LieBtrau/AMT5000-24/simulation/amplifier/Class_E_with_transistor_and_gate_driver.asc

C1: cap; 255p
C2: cap; 715p
C3: cap; 185.30p
C4: cap; 555.89p
C5: cap; 555.89p
C7: cap; 10n
D1: diode; MMSD4148
L1: ind; .33µ
L2: ind; 190n
L3: ind; 5µ
M2: nmos; irlml2060pbf
M3: nmos; irlml2060pbf
R1: res; {Rout}
R2: res; 0.1
R3: res; {Rsource}
R4: res; 1k
R5: res; 48.5k
R6: res; 1.5k
U1: TS391
V1: voltage; 0; AC 1
V2: voltage; PULSE(0 5 0 1n 1n {0.5/freq} {1/freq})
V4: voltage; SINE(6 6 10k)
V5: voltage; 1.5v
Named nets: 0, VAC, VDD, OSC, NM0S_OUT4, Vref
;ac dec 101 1meg 1g
.model SWx SW(Ron=0.1 Roff=10Meg Vt=2.5 Vh=0.5)
.tran 0 200µ 30u 1n startup
.param freq 13.56e6
.options numdgt=12
.options plotwinsize=0
.four {freq} 10 100 V(K9PDP_OUT2) V(NM0S_OUT2)
Harmonic analysis (View -> SPICE Error Log) to see the results
.inc irlml2060pbf.spi
.param Rsource=0.01 Rout=50
