LieBtrau/AMT5000-24/simulation/temperature/LM4041_Thermistor.asc

R1: res; 12.3K
R2: res; {Rthermistor}
R3: res; 10K
R4: res; 330k
R5: res; 1Meg
R6: res; 10K
U1: LM4041_N_ADJC1P233
U2: LM4041_N_ADJC1P233
V1: voltage; 10
Named nets: VCC, 0, VOUT
.op
.step param Rthermistor 1K 2K
Thermistor is 1.5K at 85°C
VOUT connected to RST input of TPS3808, which triggers at 400mV
