LieBtrau/AMT5000-24/simulation/pwm-audio/pwm-audio.asc

A1: sample
B1: bv; V=if(V(sample)>V(triangle), 1,0)
C1: cap; 51µ
C2: cap; 20µ
C3: cap; 39µF
L1: ind; 20µ
L2: ind; 51µ
L3: ind; 39µH
R1: res; 1
R2: res; 1
R3: res; 1
R4: res; 1
V1: voltage; SINE(0 {amp} {Faudio})
V2: voltage; PULSE(0 5 0 1n 1n {0.5/Fs} {1/Fs})
V3: voltage; PULSE({-amp} {amp} 0 {1/Fpwm} 1n 0 0)
Named nets: 0, triangle, sample, OUT_4o, SW, OUT_2o
.param Fs=256k
.tran 50m
.param Fpwm=48K
.param amp=1
.options plotwinsize=0
.options numdgt=12
.four {Faudio} V(out)
.param Faudio=4k
