LieBtrau/AMT5000-24/simulation/oscillator/oscillator.asc

C1: cap; 15p
C2: cap; 10n
C3: cap; 27n
C4: cap; 10n
C6: cap; 100n
C7: cap; 15p
R1: res; 22
R2: res; 10
V1: voltage; PULSE(0 3.3 0 1n 1n {0.5/freq} {1/freq})
Named nets: 0
.param freq=25Meg
.tran 0 2u 1u
