LieBtrau/AMT5000-24/simulation/amplifier/Class_E_with_transistor.asc

C1: cap; 260p
C2: cap; 700p
C3: cap; 185.30p
C4: cap; 555.89p
C5: cap; 555.89p
C6: cap; 234p
C7: cap; 710p
C8: cap; 185.30p
C9: cap; 555.89p
C10: cap; 555.89p
C21: cap; 278p
C22: cap; 700p
C23: cap; 185.30p
C24: cap; 555.89p
C25: cap; 555.89p
L1: ind; .33µ
L2: ind; 190n
L3: ind; 5µ
L4: ind; .33µ
L5: ind; 190n
L6: ind; 5µ
L11: ind; .33µ
L12: ind; 190n
L13: ind; 5µ
M1: nmos; irlml2060pbf
M2: nmos; irlml2060pbf
M3: nmos; irlml2060pbf
M4: nmos; irlml0060trpbf
R1: res; {Rout}
R2: res; {Rout}
R3: res; {Rsource}
R4: res; {Rsource}
R5: res; {Rout}
R6: res; {Rsource}
V1: voltage; 0; AC 1
V2: voltage; PULSE(0 5 0 1n 1n {0.5/freq} {1/freq})
V4: voltage; 12
Named nets: 0, VAC, VDD, OSC, NM0S_OUT3, NM0S_OUT4, NM0S_OUT5
;ac dec 101 1meg 1g
.model SWx SW(Ron=0.1 Roff=10Meg Vt=2.5 Vh=0.5)
.tran 0 30.5u 30u 1n startup
.param freq 13.56e6
.options numdgt=12
.options plotwinsize=0
.four {freq} 10 100 V(K9PDP_OUT2) V(NM0S_OUT2)
Harmonic analysis (View -> SPICE Error Log) to see the results
.inc irlml2060pbf.spi
.inc irlml0060trpbf.spi
.param Rsource 0.1
.param Rout=50
