LieBtrau/AMT5000-24/simulation/temperature/opamp_current_source.asc

R1: res; {Rthermistor}
R2: res; 20K
R3: res; 12K
R4: res; 10K
R5: res; 20k
R6: res; 8.2k
R7: res; 10K
U1: OP07
U2: TLV431
U3: TS391
V1: voltage; 5V
Named nets: VCC, 0, VREF, VFB, VCOMPOUT
.op
;.dc V1 3 6
.param Rthermistor=10K
.step param Rthermistor 1.5K 10K 50
2-wire measurement of thermistor is independent of ground bounce.
