LieBtrau/AMT5000-24/simulation/temperature/thermistor_comparator.asc

R1: res
R8: res; {Rthermistor}
R9: res; 13K
R10: res; 10K
R11: res; 1K
R12: res; 12K
R14: res; 10K
R15: res; 10K
U4: TLV431
U5: TLV431
U6: TS391
V1: voltage; 5V
Named nets: VCC, 0
.op
;.dc V1 3 6
.param Rthermistor=10K
.step param Rthermistor 500 1.5K
2-wire measurement of thermistor is independent of ground bounce.
Result is independent of VCC
Thermistor current must be < 100µA
Example thermistor : NCP18XH103F03RB
Comparator output low when Rthermistor < 1K
Is this circuit a good idea?  It will be harder to thermally couple the thermistor when it's not electrically coupled.
Hysteresis
