LieBtrau/AMT5000-24/simulation/amplifier/Class_E.asc

C1: cap; 129p
C2: cap; 155.1p
C3: cap; 172.73p
C4: cap; 1075p
C5: cap; 704.2p
C6: cap; 230.12p
C7: cap; 987.31p
C8: cap; 185.30p
C9: cap; 555.89p
C10: cap; 555.89p
C11: cap; 150p
C12: cap; 154p
C13: cap; 172.73p
C14: cap; 1075p
C15: cap; 704.2p
C16: cap; 307p
C17: cap; 690p
C18: cap; 185.30p
C19: cap; 555.89p
C20: cap; 555.89p
L1: ind; .33µ
L2: ind; 1.11µ
L3: ind; 200n
L4: ind; 190n
L5: ind; 1.11µ
L6: ind; 200n
L7: ind; .33µ
L8: ind; 190n
L9: ind; 5µ
L10: ind; 5µ
R1: res; 16.7
R2: res; 50
R3: res; 50
R4: res; 50
S1: sw; SWx
S2: sw; SWx
V1: voltage; 0; AC 1
V2: voltage; PULSE(0 5 0 1n 1n {0.5/freq} {1/freq})
V4: voltage; 12
Named nets: 0, K9PDP_OUT, NM0S_OUT, VAC, K9PDP_OUT2, NM0S_OUT2, VDD, OSC
;ac dec 101 1meg 1g
K9PDP Design
NM0S Design
.model SWx SW(Ron=0.1 Roff=10Meg Vt=2.5 Vh=0.5)
.tran 0 30.5u 30u 1n startup
.param freq 13.56e6
.options numdgt=12
.options plotwinsize=0
.four {freq} 10 100 V(K9PDP_OUT2) V(NM0S_OUT2)
Harmonic analysis (View -> SPICE Error Log) to see the results
